frankyhub/Greifarm_Servo/pic/EEZYBOTARM_MK2_004.png

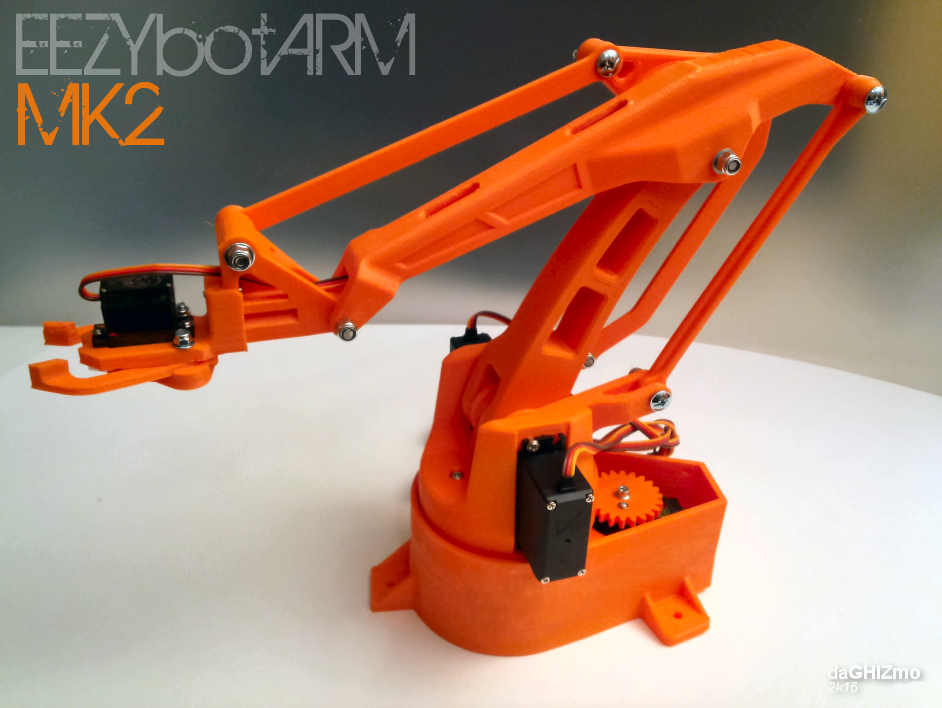
pic/EEZYBOTARM_MK2_004.png
