frankyhub/Greifarm_Servo/pic/EEZYBOTARM_MK2_005.png

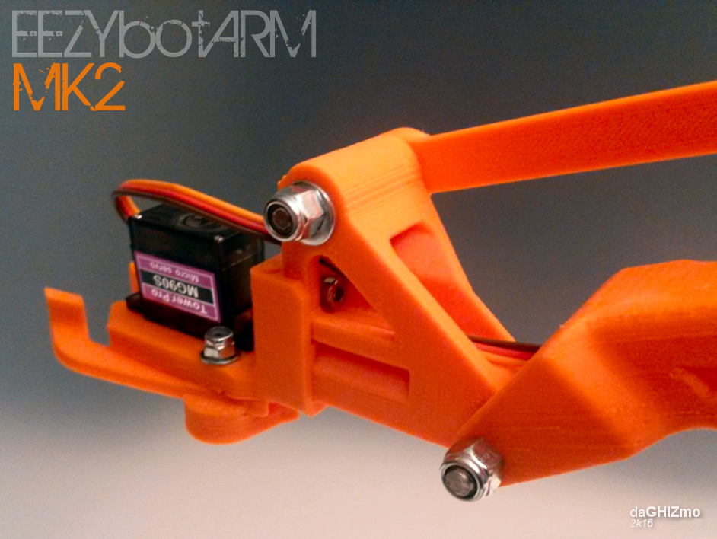
pic/EEZYBOTARM_MK2_005.png
