frankyhub/Greifarm_Servo/pic/EEZYBOTARM_MK2_006.png

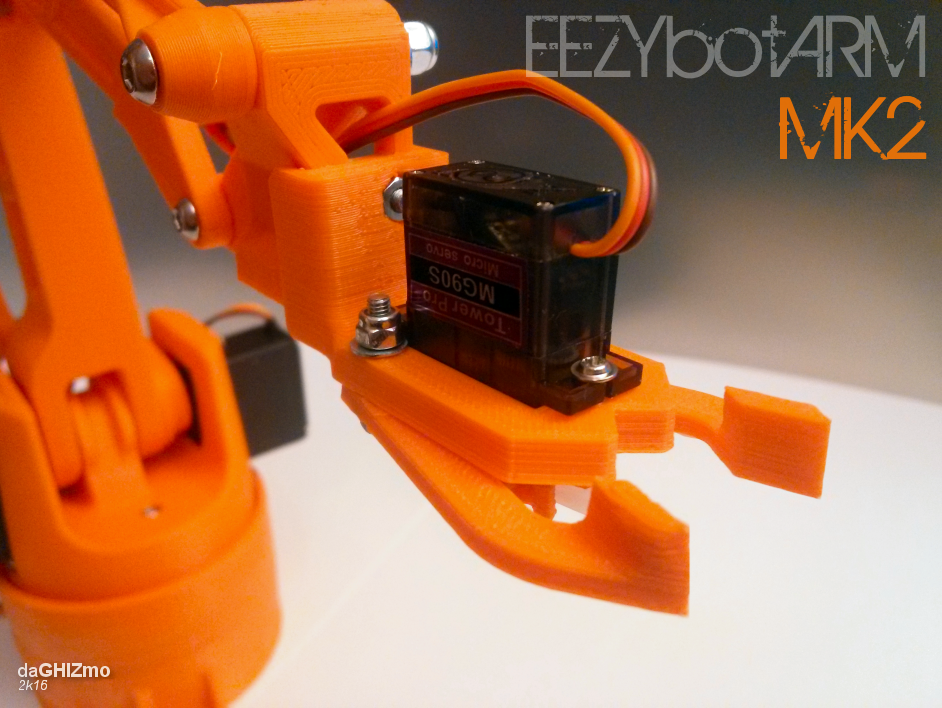
pic/EEZYBOTARM_MK2_006.png
