frankyhub/Greifarm_Servo/pic/EEZYBOTARM_MK2_007.png

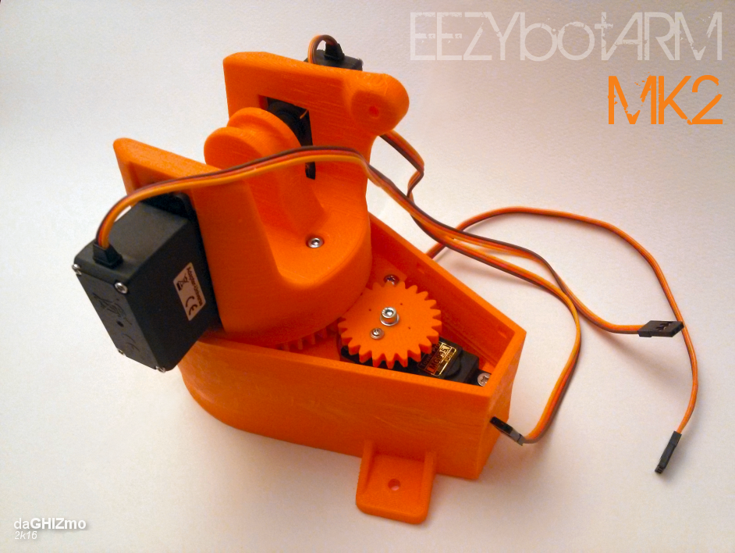
pic/EEZYBOTARM_MK2_007.png
