frankyhub/Greifarm_Servo/pic/EEZYBOTARM_MK2_008.png

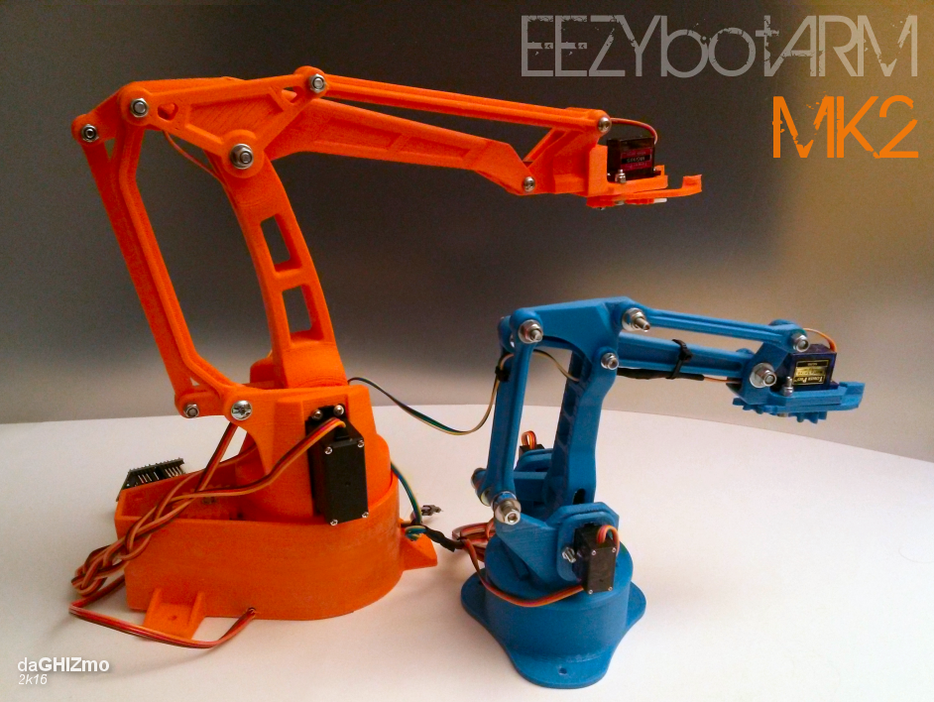
pic/EEZYBOTARM_MK2_008.png
