frankyhub/Greifarm_Servo/pic/EEZYBOTARM_MK2_009.png

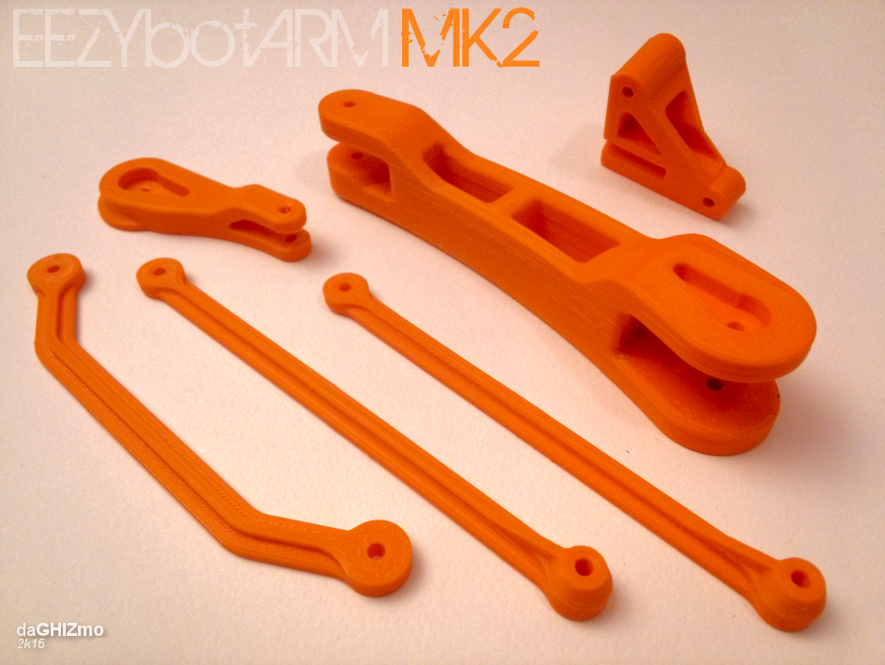
pic/EEZYBOTARM_MK2_009.png
