frankyhub/Greifarm_Servo/pic/EEZYBOTARM_MK2_012.png

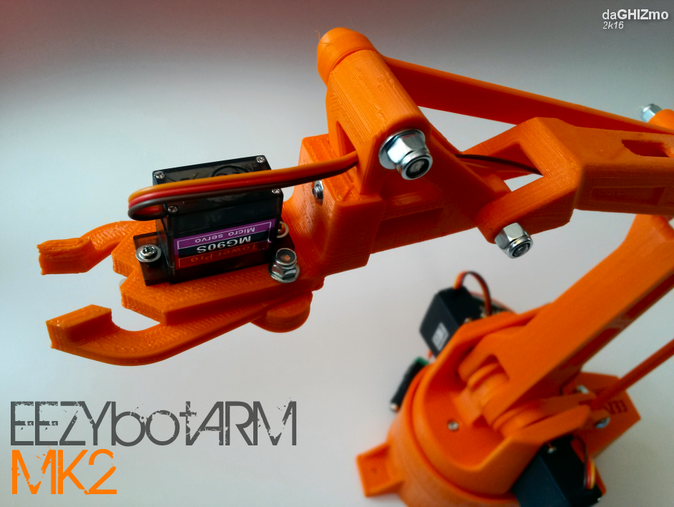
pic/EEZYBOTARM_MK2_012.png
