frankyhub/Greifarm_Servo/pic/EEZYBOTARM_MK2_014.png

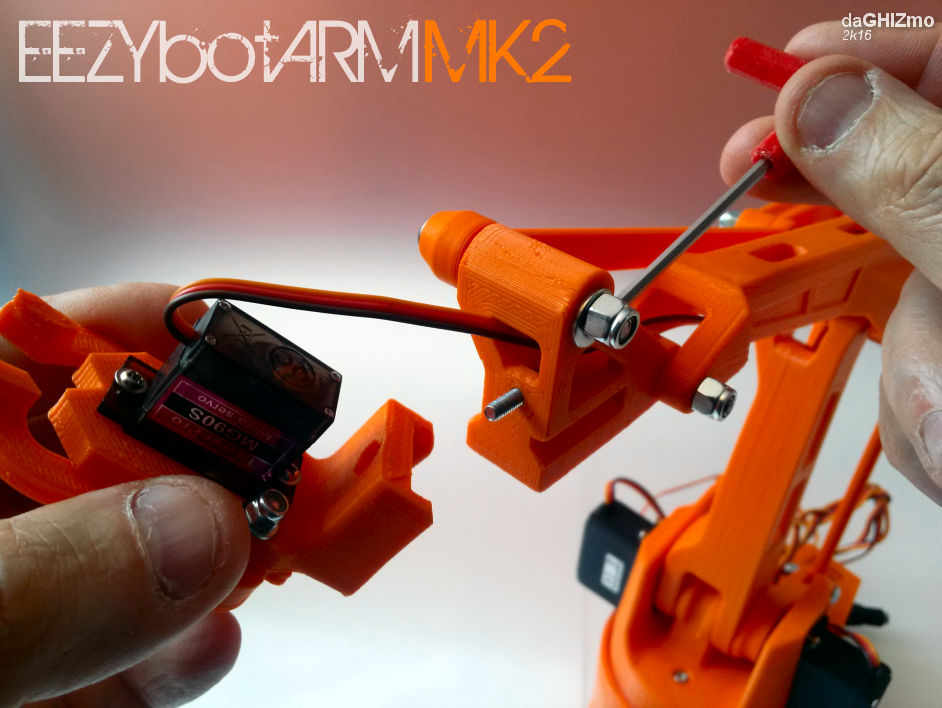
pic/EEZYBOTARM_MK2_014.png
