frankyhub/Greifarm_Servo/pic/EEZYBOTARM_MK2_015.png

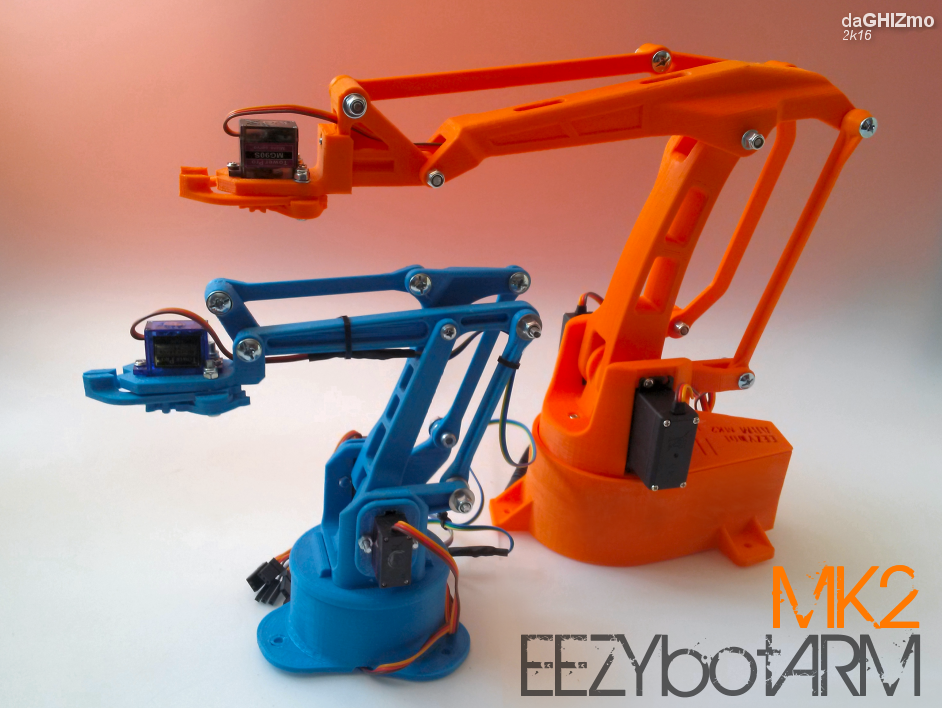
pic/EEZYBOTARM_MK2_015.png
