frankyhub/Greifarm_Servo/pic/EEZYBOTARM_MK2_016.png

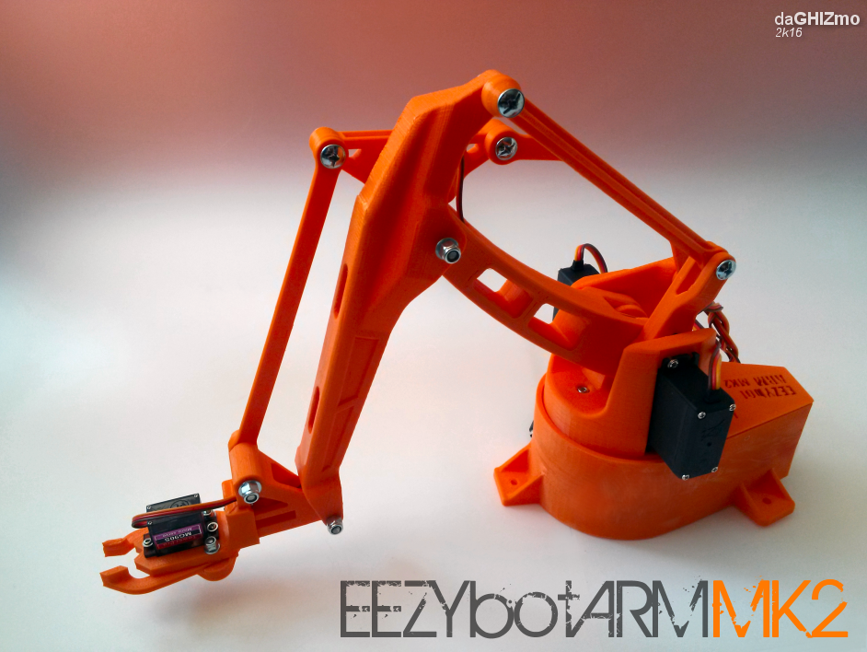
pic/EEZYBOTARM_MK2_016.png
