frankyhub/Greifarm_Servo/pic/EEZYBOTARM_MK2_018.png

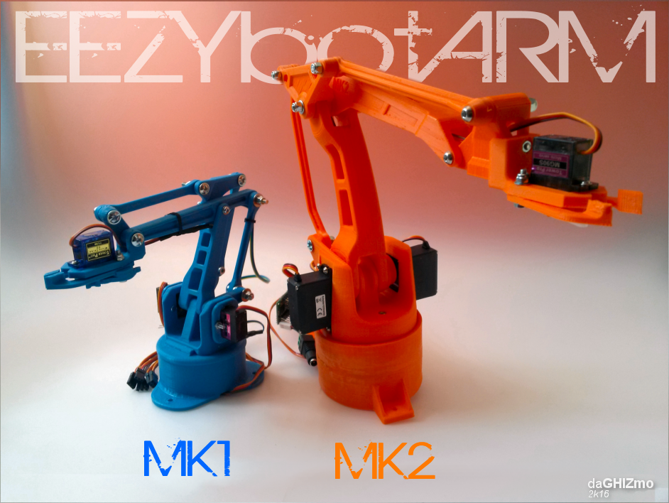
pic/EEZYBOTARM_MK2_018.png
