frankyhub/Greifarm_Servo/pic/EEZYBOTARM_MK2_019.png

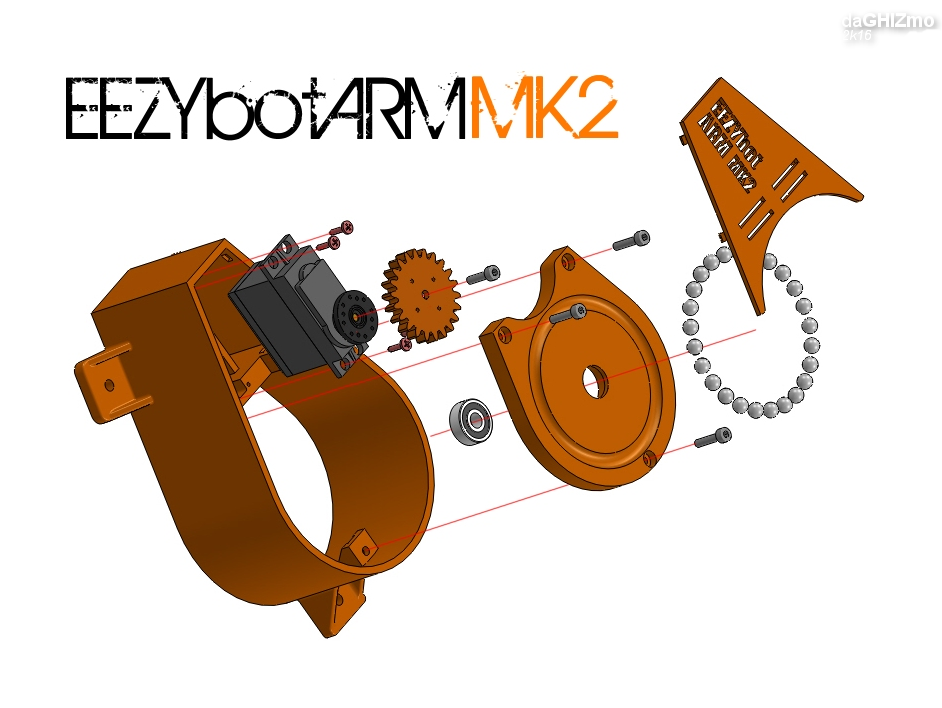
pic/EEZYBOTARM_MK2_019.png
