frankyhub/Greifarm_Servo/pic/EEZYBOTARM_MK2_020.png

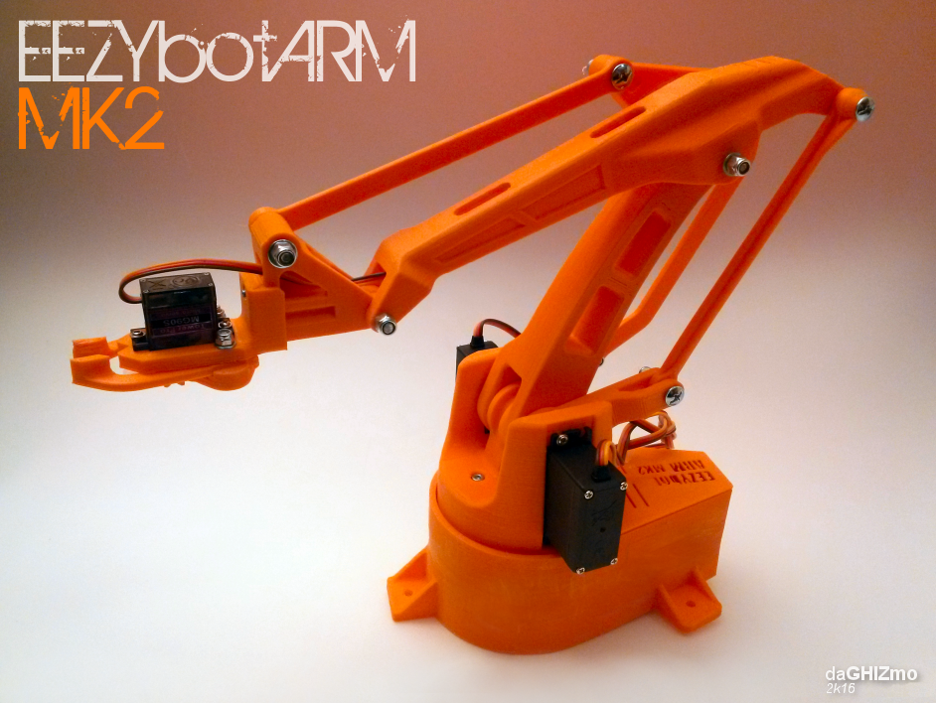
pic/EEZYBOTARM_MK2_020.png
