frankyhub/Greifarm_Servo/pic/MK_2_2.png

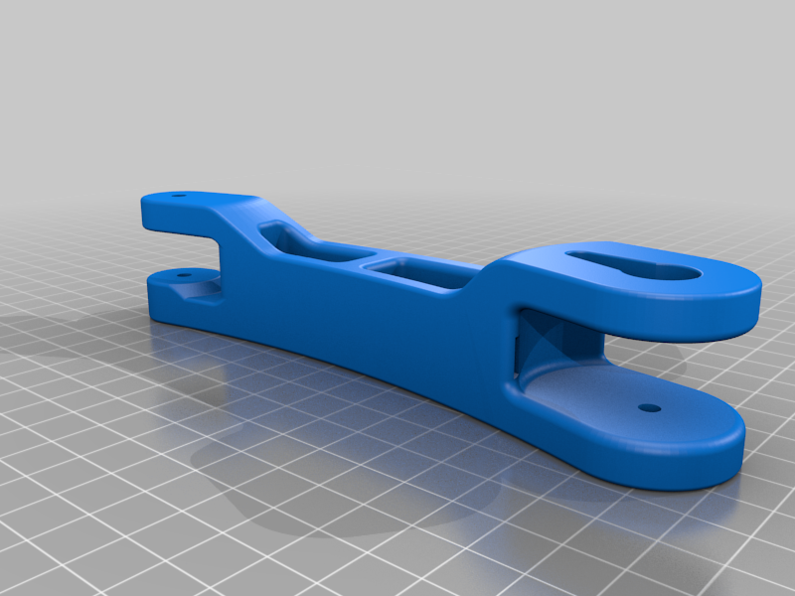
pic/MK_2_2.png
