frankyhub/Greifarm_Servo/pic/MK_2_4.png

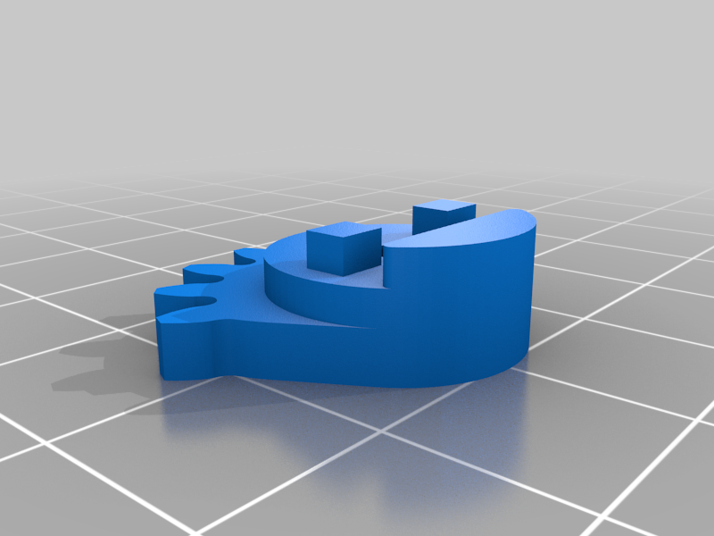
pic/MK_2_4.png
