frankyhub/Greifarm_Servo/pic/MK_2_5.png

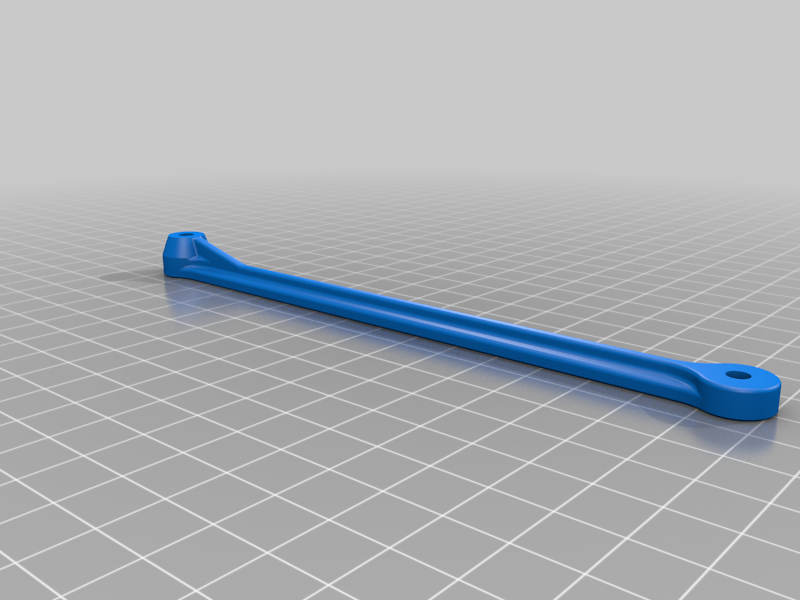
pic/MK_2_5.png
