frankyhub/Greifarm_Servo/pic/MK_2_6.png

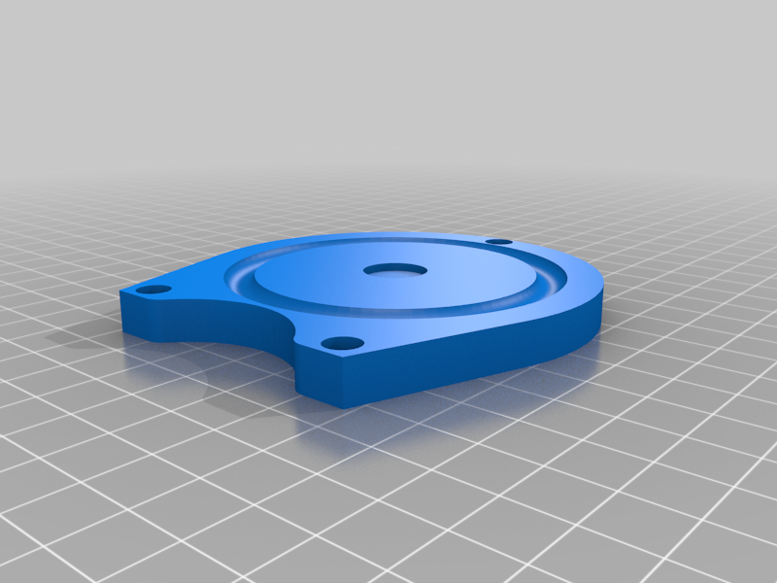
pic/MK_2_6.png
