frankyhub/Greifarm_Servo/pic/MK_2_7.png

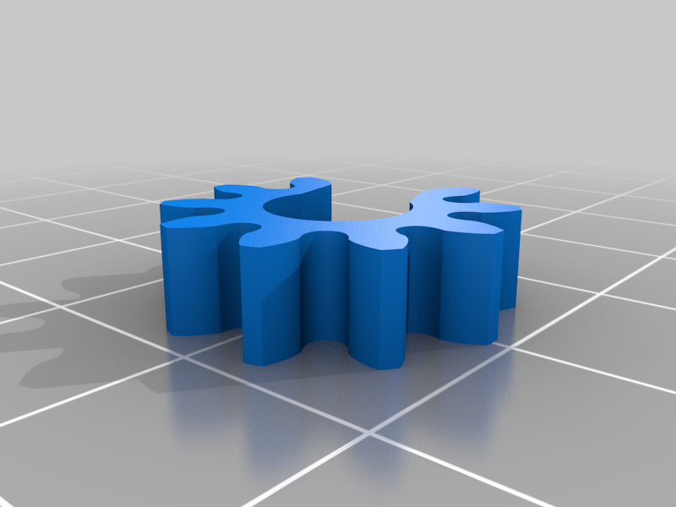
pic/MK_2_7.png
