frankyhub/Greifarm_Servo/pic/MK_2_8.png

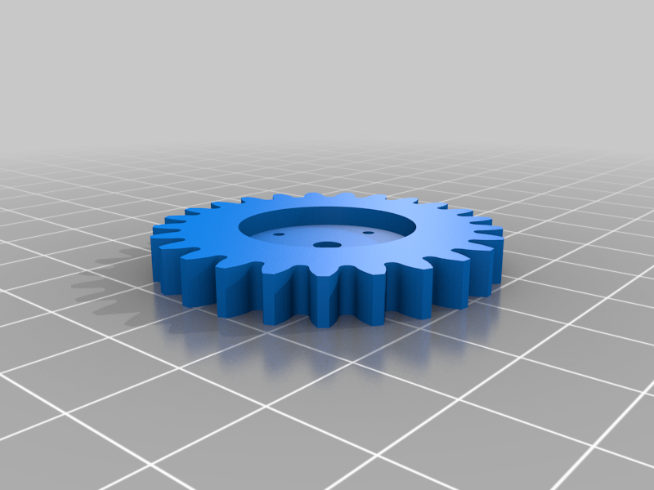
pic/MK_2_8.png
