frankyhub/Greifarm_Servo/pic/MK_2_9.png

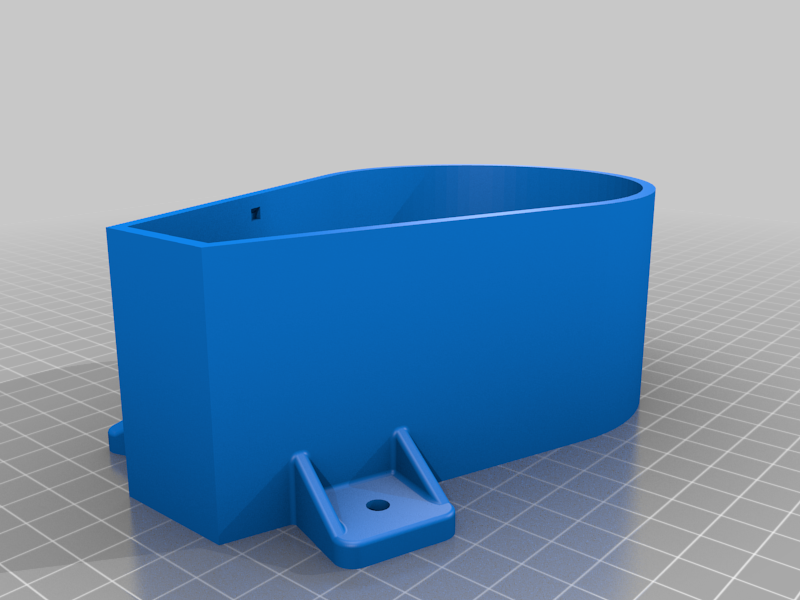
pic/MK_2_9.png
