frankyhub/Greifarm_Servo/pic/MK_2_10.png

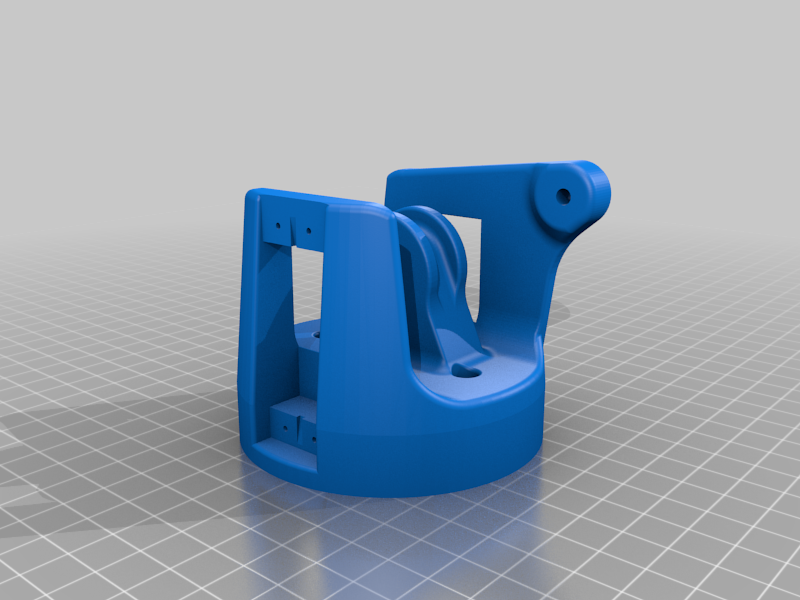
pic/MK_2_10.png
