frankyhub/Greifarm_Servo/pic/MK_2_11.png

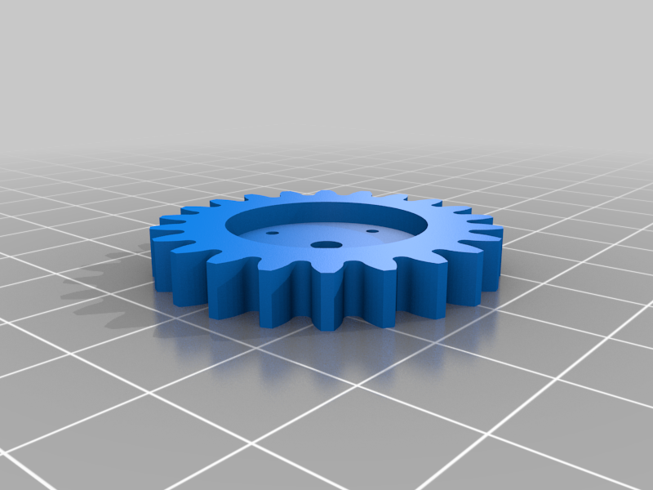
pic/MK_2_11.png
