frankyhub/Greifarm_Servo/pic/MK_2_12.png

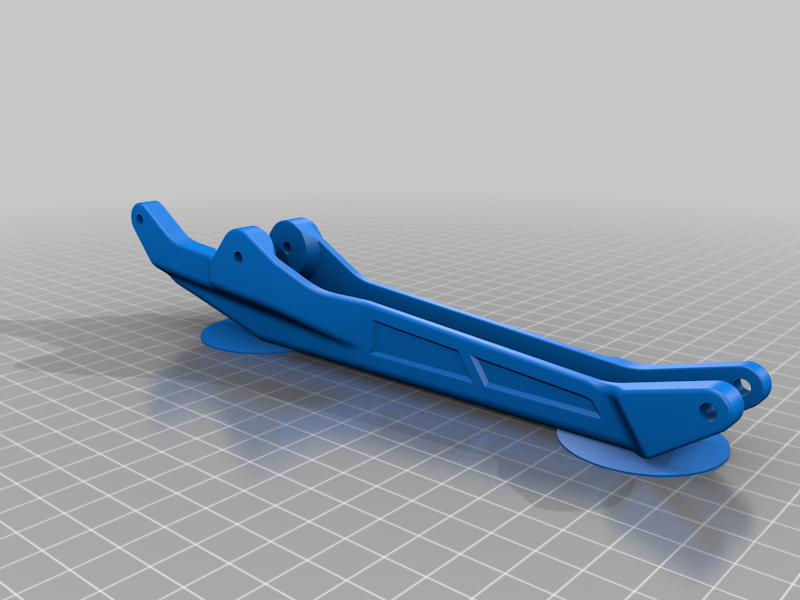
pic/MK_2_12.png
