frankyhub/Greifarm_Servo/pic/MK_2_13.png

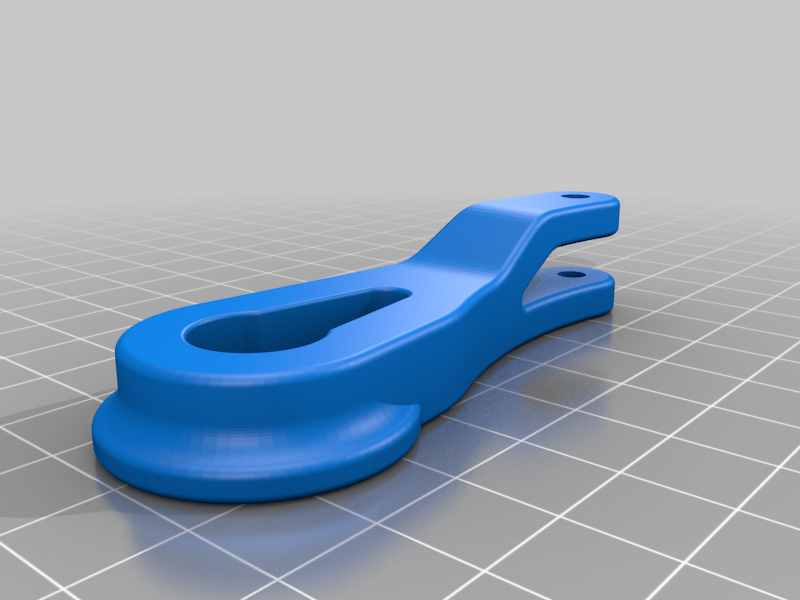
pic/MK_2_13.png
