frankyhub/Greifarm_Servo/pic/MK_2_14.png

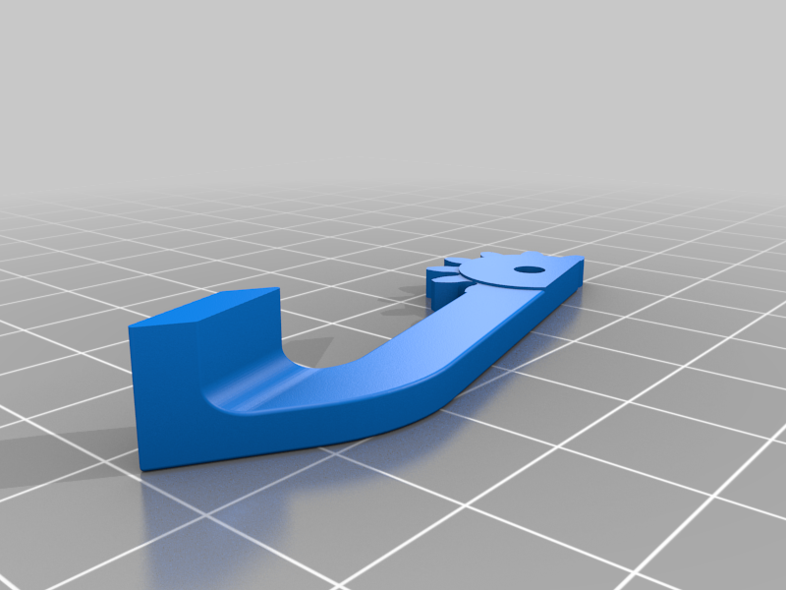
pic/MK_2_14.png
