frankyhub/Greifarm_Servo/pic/MK_2_16.png

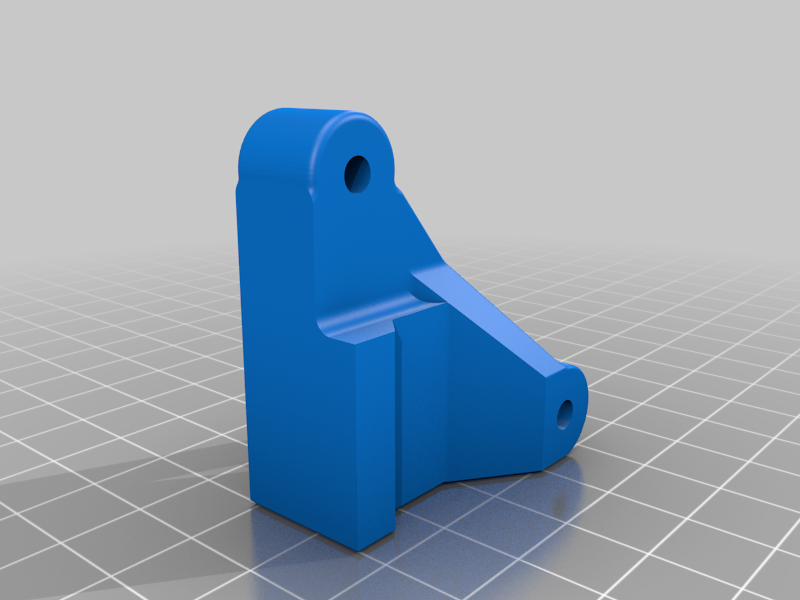
pic/MK_2_16.png
