frankyhub/Greifarm_Servo/pic/MK_2_17.png

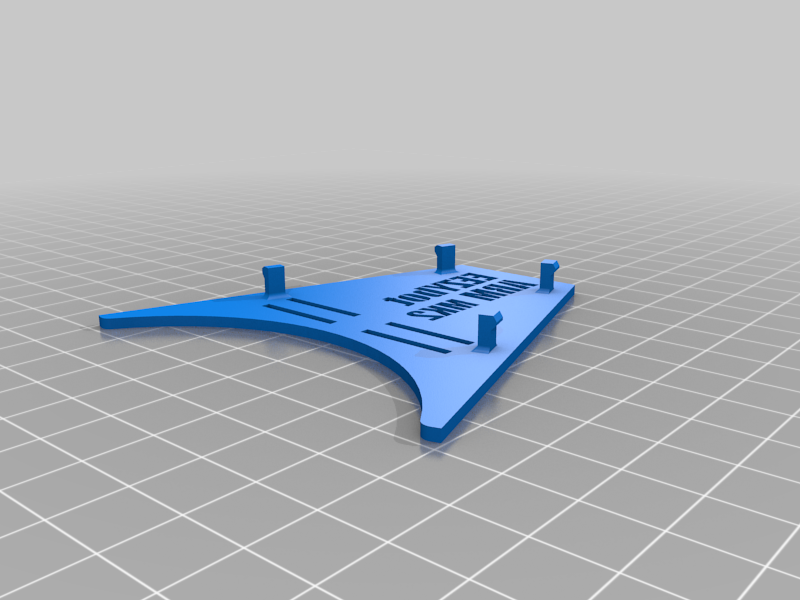
pic/MK_2_17.png
