frankyhub/Greifarm_Servo/pic/MK_2_22.png

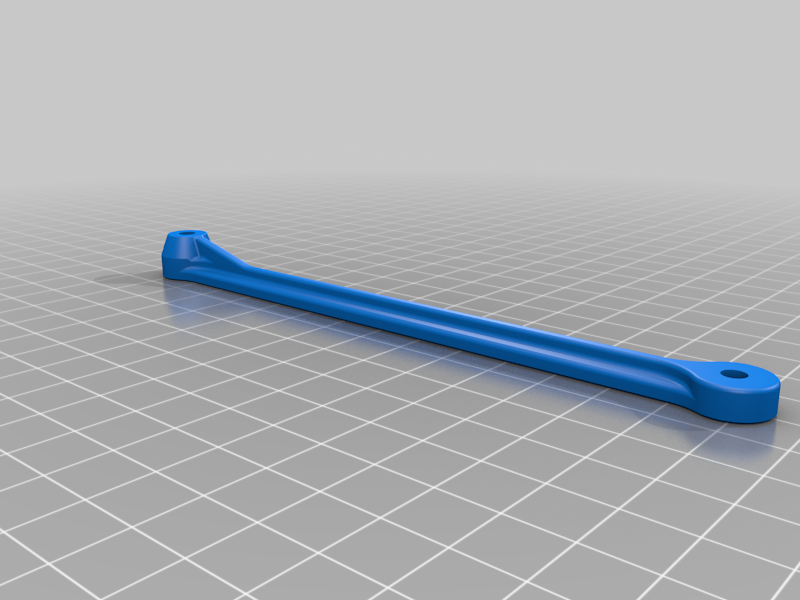
pic/MK_2_22.png
