frankyhub/Greifarm_Servo/stl/EBAmk2_004_link135.STL

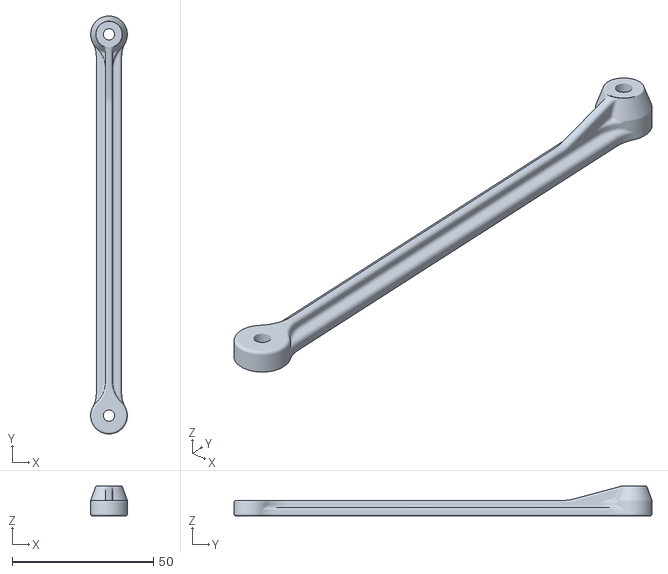
[picture p76: CAD file, 2024-05-29]
stl/EBAmk2_004_link135.STL
13.0 x 148.0 x 10.5
