frankyhub/Greifarm_Servo/stl/EBAmk2_013_lower_base.STL

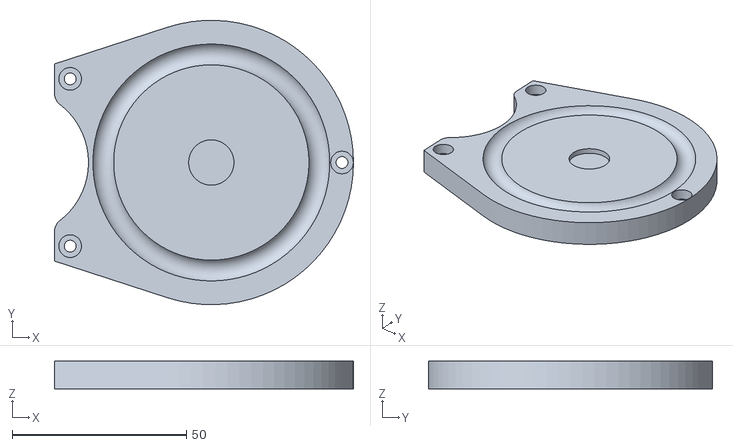
[picture p77: CAD file, 2024-05-29]
stl/EBAmk2_013_lower_base.STL
85.8 x 81.6 x 8.00
