frankyhub/Greifarm_Servo/stl/EBAmk2_014_claw_base.STL

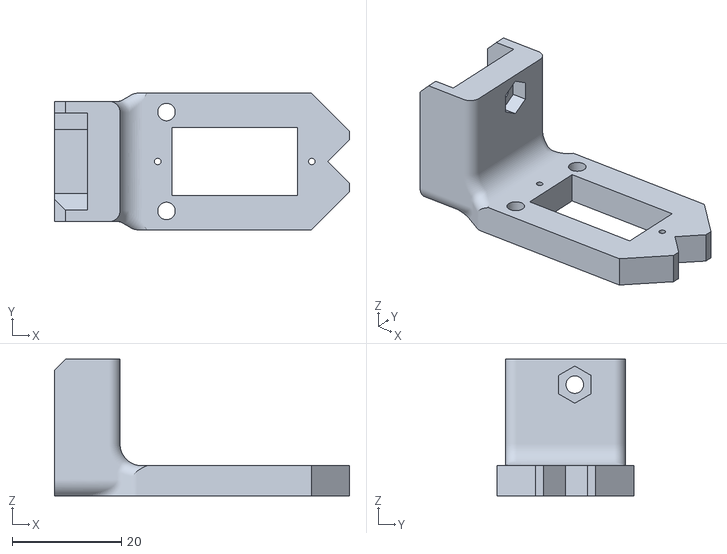
[picture p78: CAD file, 2024-05-29]
stl/EBAmk2_014_claw_base.STL
54.0 x 25.0 x 25.0
