frankyhub/Greifarm_Servo/stl/EBAmk2_014_claw_std.step

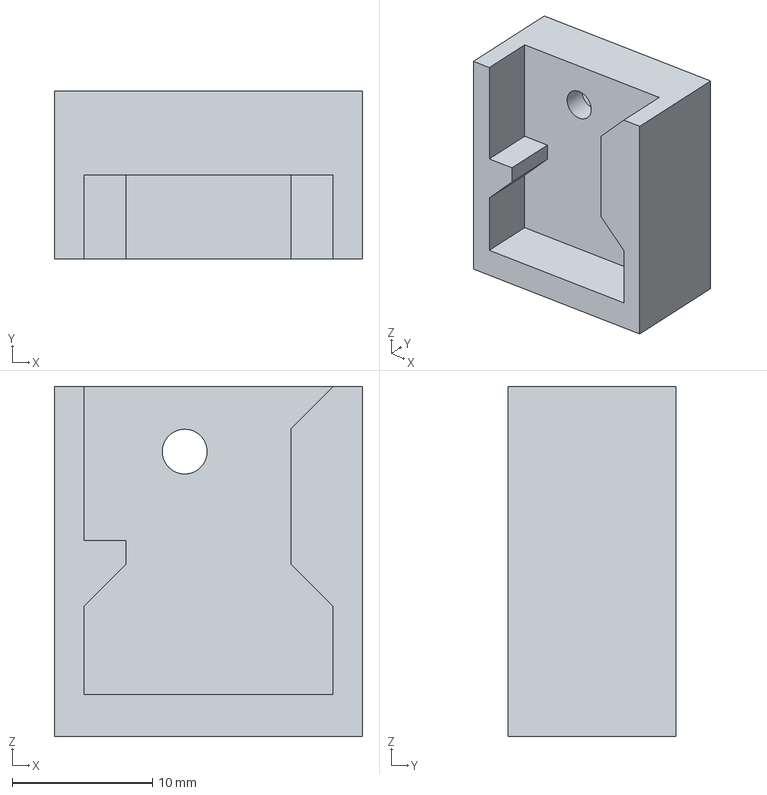
[picture p79: CAD file, 2024-05-29]
stl/EBAmk2_014_claw_std.step
22.0 x 12.0 x 25.0 mm
