frankyhub/Greifarm_Servo/stl/EBAmk2_018_claw_gear_driven.STL

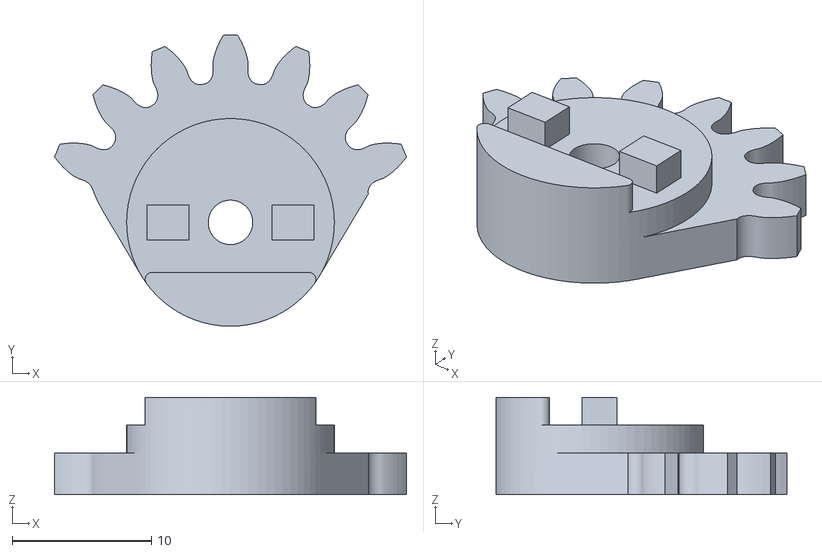
[picture p80: CAD file, 2024-05-29]
stl/EBAmk2_018_claw_gear_driven.STL
25.3 x 21.0 x 7.00
