frankyhub/Greifarm_Servo/stl/EBAmk2_007_trialink.STL

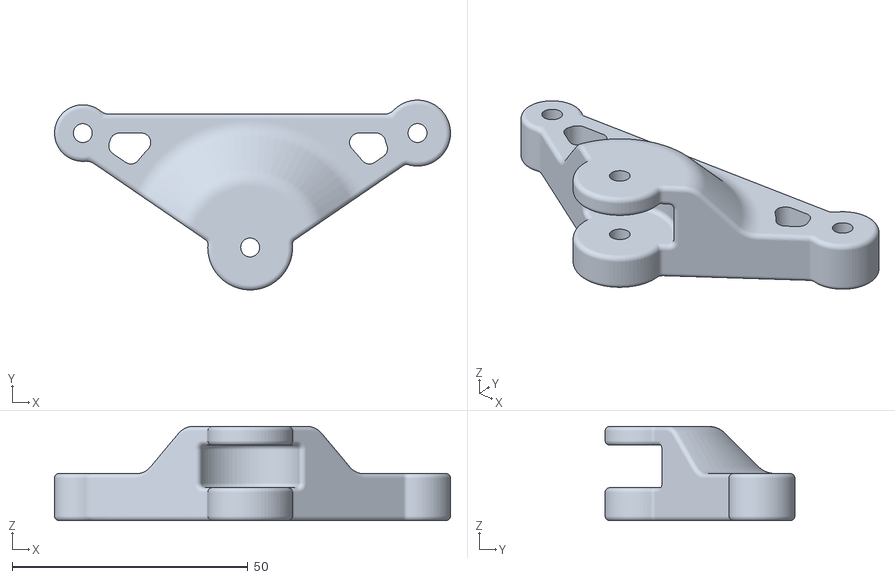
[picture p81: CAD file, 2024-05-29]
stl/EBAmk2_007_trialink.STL
84.0 x 40.3 x 20.0
