frankyhub/Greifarm_Servo/stl/EBAmk2_008_link147_new.STL

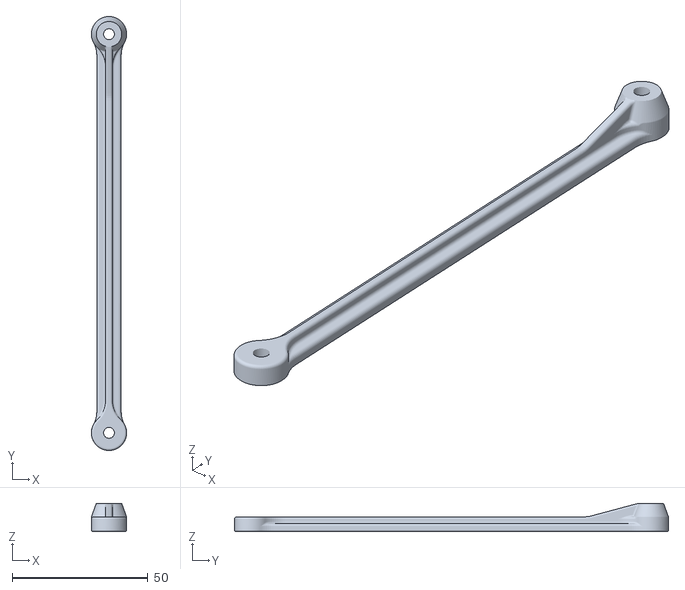
[picture p82: CAD file, 2024-05-29]
stl/EBAmk2_008_link147_new.STL
13.0 x 160.0 x 10.5
