frankyhub/Greifarm_Servo/stl/EBAmk2_006_horarm__.STL

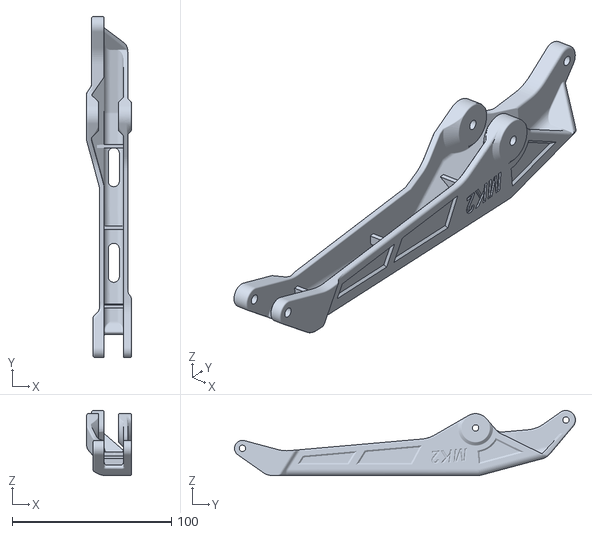
[picture p83: CAD file, 2024-05-29]
stl/EBAmk2_006_horarm__.STL
28.0 x 214.2 x 40.9
