frankyhub/Greifarm_Servo/stl/EBAmk2_009_trialinkfront.STL

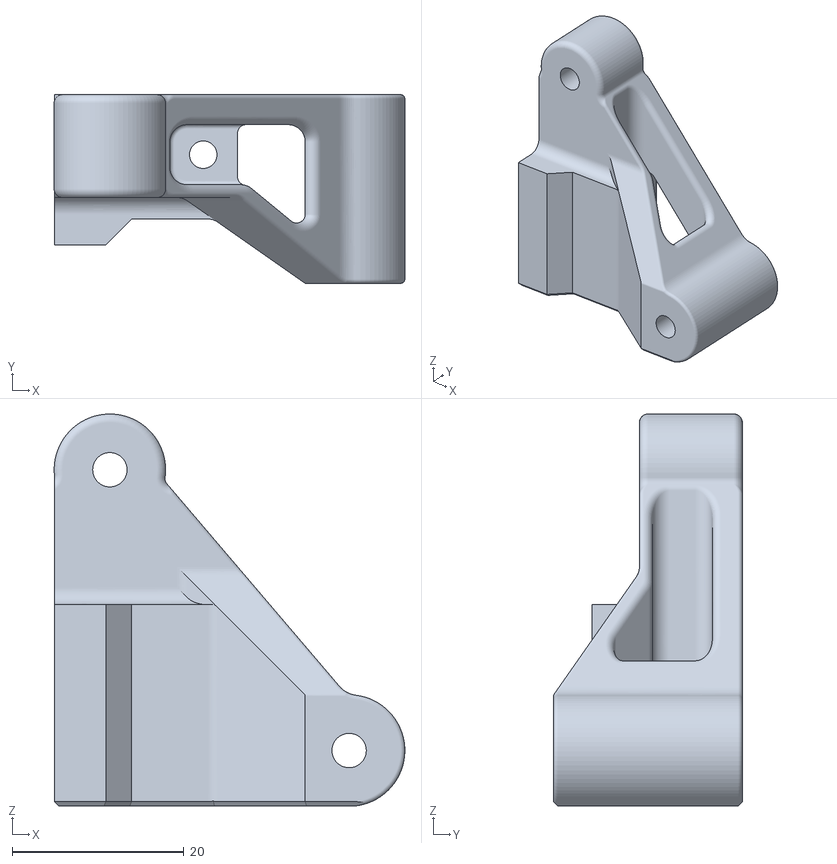
[picture p84: CAD file, 2024-05-29]
stl/EBAmk2_009_trialinkfront.STL
40.9 x 22.0 x 45.7
