frankyhub/Greifarm_Servo/stl/EBAmk2_005_link135angled.STL

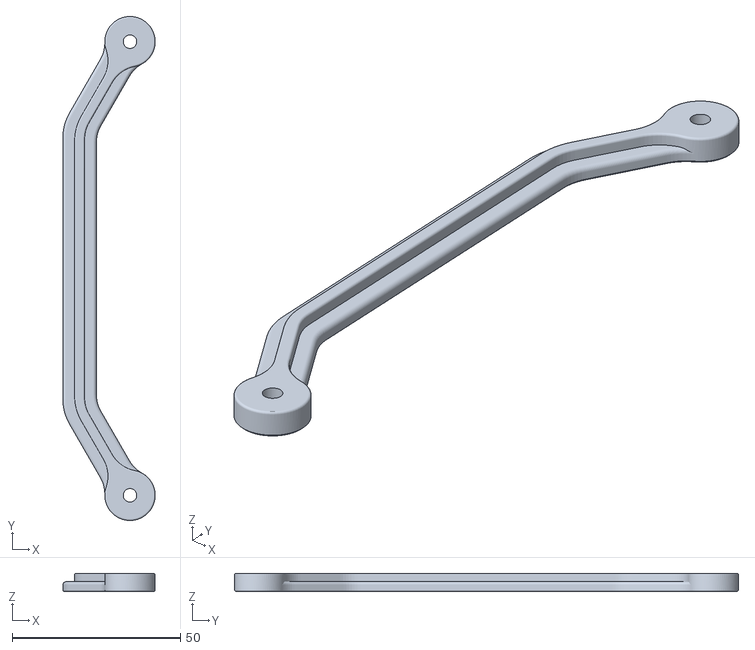
[picture p85: CAD file, 2024-05-29]
stl/EBAmk2_005_link135angled.STL
27.5 x 150.0 x 5.50
